andykarpov/karabas-nano/docs/photos/karabas-nano-revG-top.png

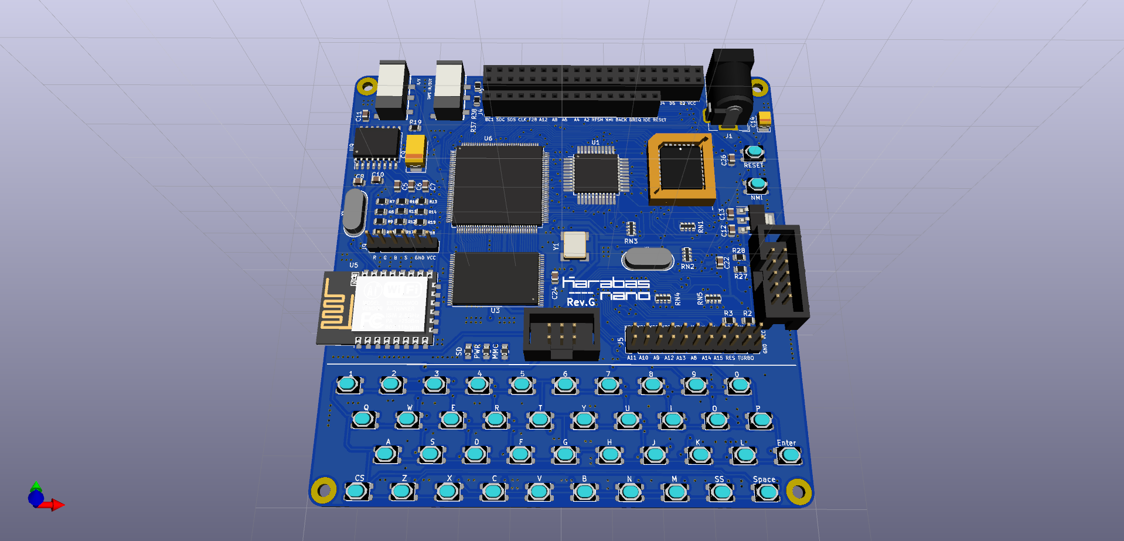
docs/photos/karabas-nano-revG-top.png
