andykarpov/karabas-nano/docs/photos/revC-1.png

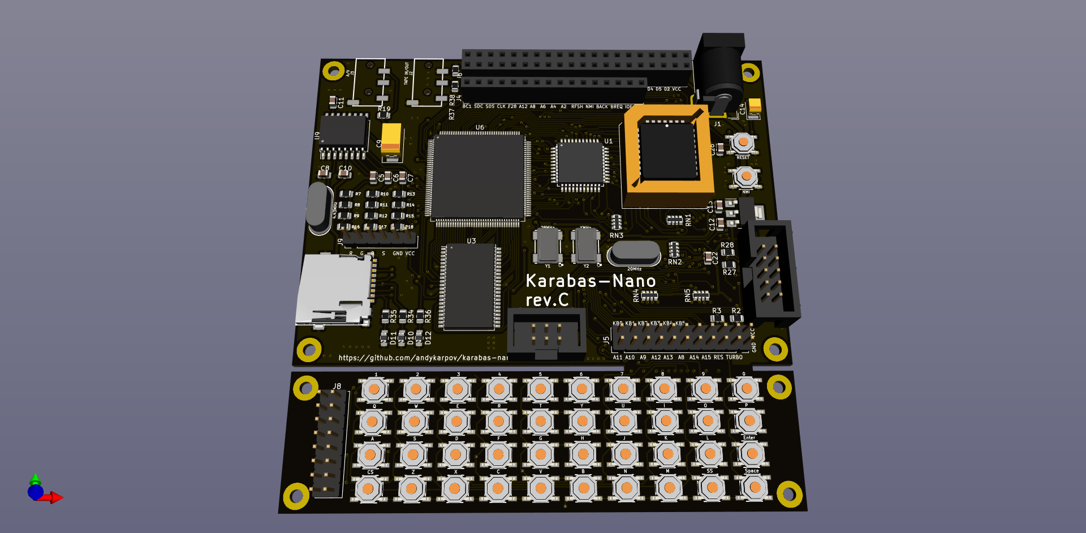
docs/photos/revC-1.png
