andykarpov/karabas-nano/docs/photos/revC-2.png

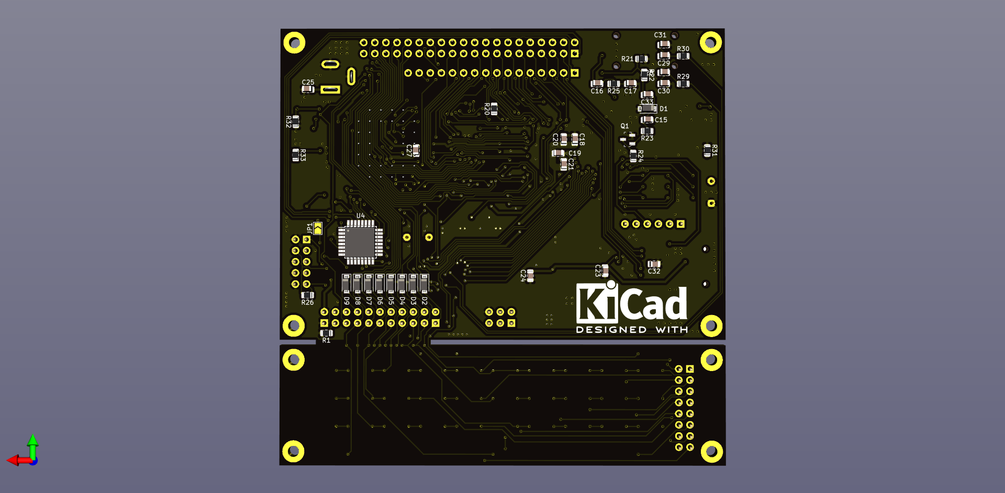
docs/photos/revC-2.png
