andykarpov/karabas-nano/docs/photos/revD-2.png

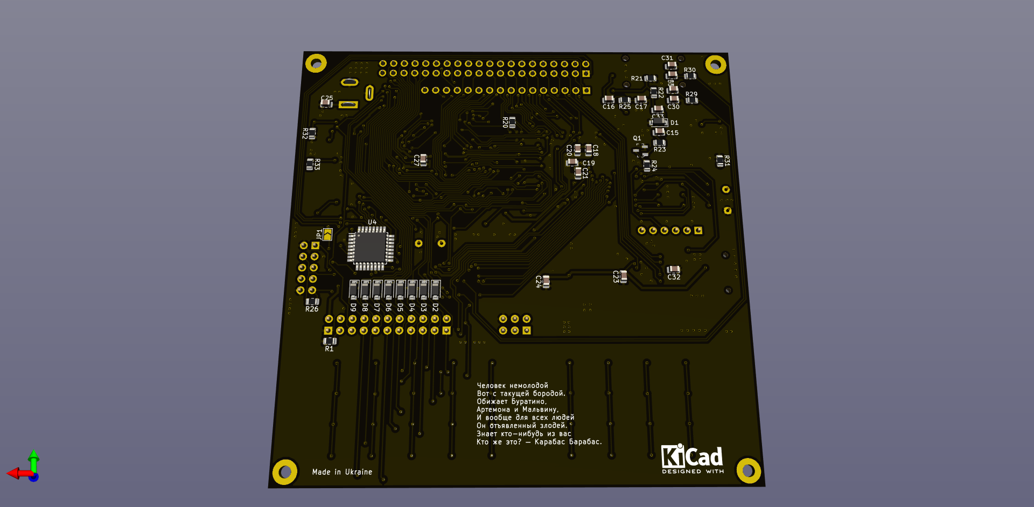
docs/photos/revD-2.png
