andykarpov/karabas-nano/docs/photos/revF-bottom.png

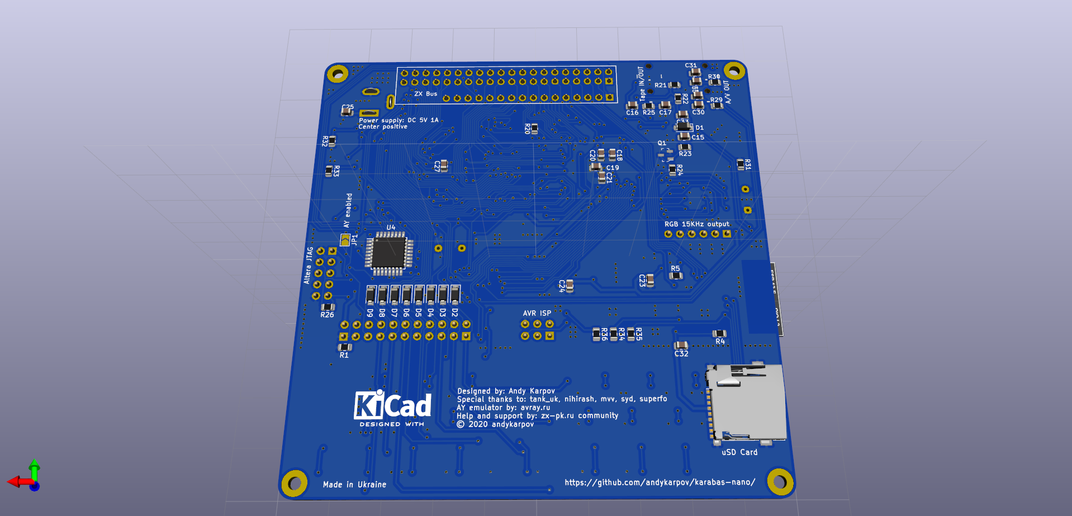
docs/photos/revF-bottom.png
